Work-KewalShah/Countdown-Timer-V1/images/Countdown_Timer_Front.png

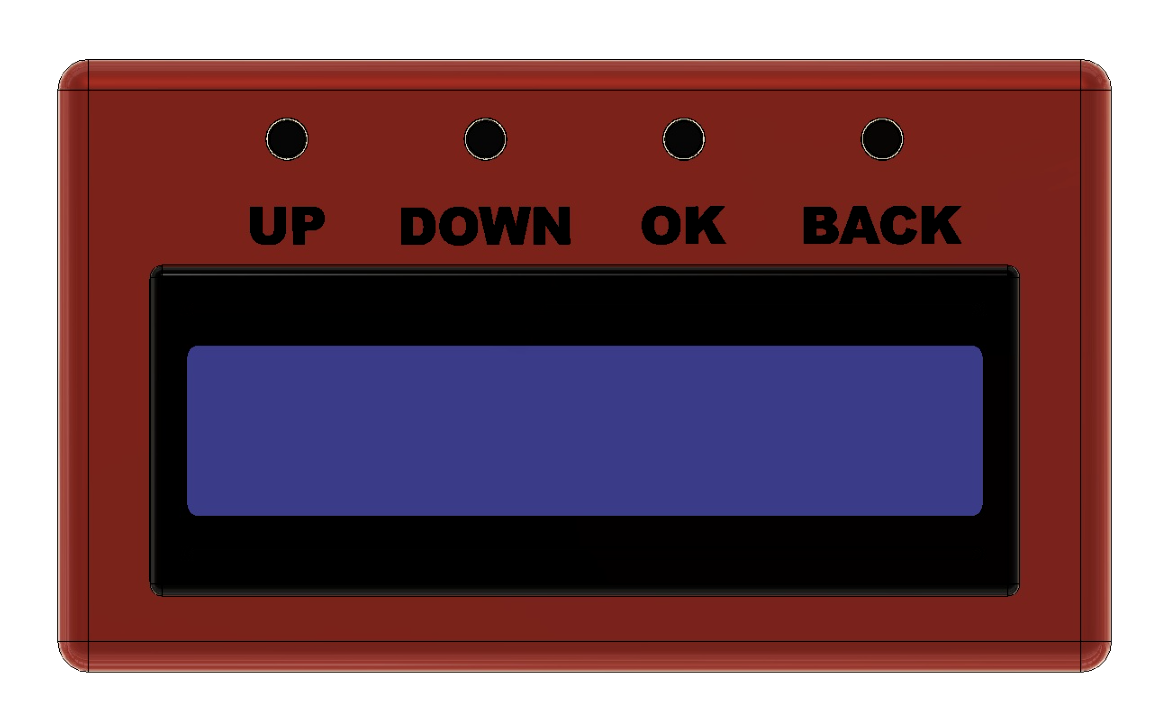
images/Countdown_Timer_Front.png
