Work-KewalShah/Countdown-Timer-V1/wiring/Countdown_Timer_V1_Wiring_Diagram.png

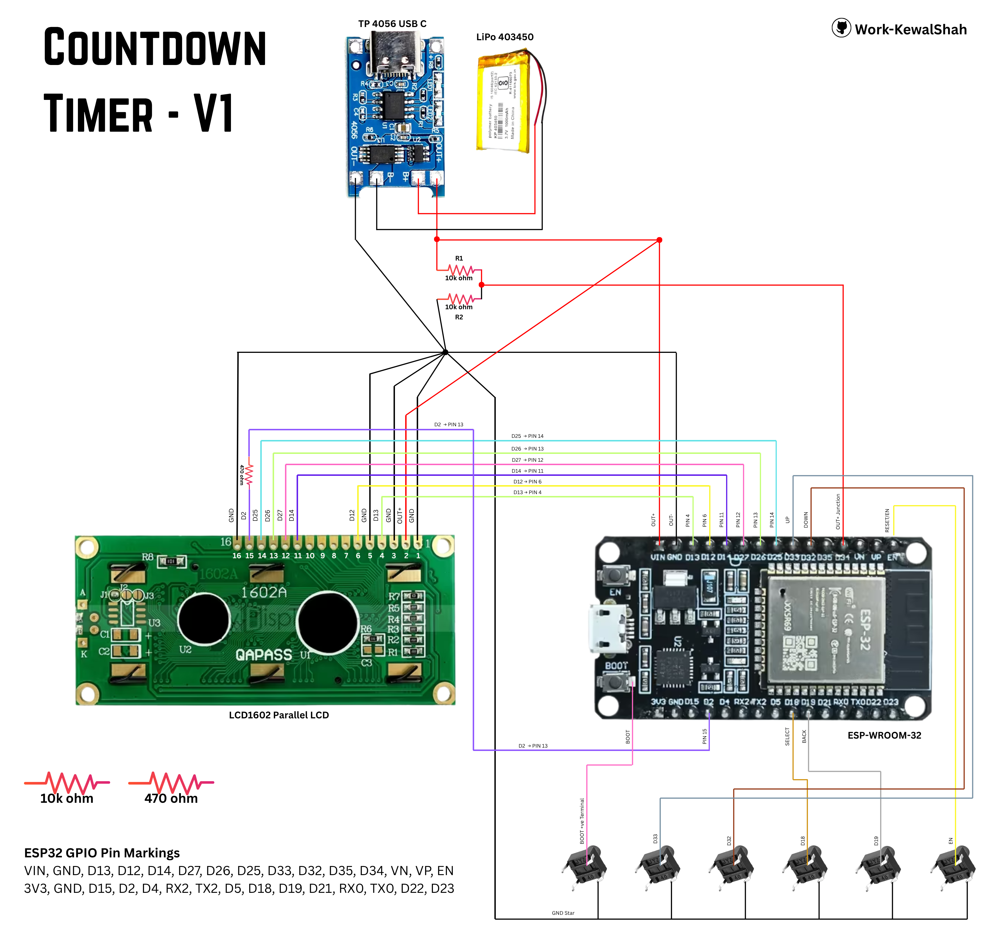
wiring/Countdown_Timer_V1_Wiring_Diagram.png
